AaronC81/delta-pico/res/pc_connection.png

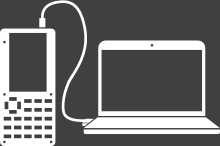
res/pc_connection.png
